yuanb/dd20emu/capture/WRData flux.png

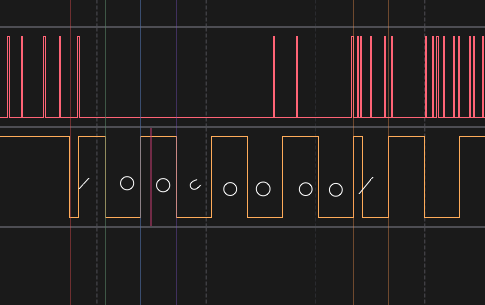
capture/WRData flux.png
