yuanb/dd20emu/dd20emu/rddata.ino

/*
    DD-20 emulator
    Copyright (C) 2020-2023 https://github.com/yuanb/dd20emu

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
    You should have received a copy of the GNU General Public License
    along with this program.  If not, see <https://www.gnu.org/licenses/>.
*/

//Tested values
//FM encoded 0 : ___n__________n___ : 1us + 31.2us + 1us (next bit)
//FM encoded 1 : ___n___n______n___ : 1us + 11 us + 1us + 19.2 us + 1us (next bit)

#define _delayNanoseconds(__ns)     __builtin_avr_delay_cycles( (double)(F_CPU)*((double)__ns)/1.0e9 /*+ 0.5 */)

#define delay_1us     _delayNanoseconds(1000)
#define delay_11us    _delayNanoseconds(11000)
#define delay_19_2us  _delayNanoseconds(19200)
#define delay_31_2us  _delayNanoseconds(31200)
#define pulse_1us   RD_HIGH; delay_1us; RD_LOW

#define RD_DATA_MASK   (1<<RD_DATA_BIT)
#define RD_HIGH   PORT_RDDATA |= RD_DATA_MASK;
#define RD_LOW    PORT_RDDATA &= ~RD_DATA_MASK;

#define FM_BIT_1  delay_11us; pulse_1us; delay_19_2us;
#define FM_BIT_0  delay_31_2us;

#define FM_ENCODE_BIT(v,m) {  if (v & m) { FM_BIT_1; } else { FM_BIT_0; } }
#define FM_OUTPUT_BIT(v,m) { pulse_1us; FM_ENCODE_BIT(v,m); }

extern uint8_t fdc_sector[SECSIZE_VZ];
extern vzdisk* vzdsk;

const uint8_t bitmask[8] = {
  0b10000000,
  0b01000000,
  0b00100000,
  0b00010000,
  0b00001000,
  0b00000100,
  0b00000010,
  0b00000001
};

bool handle_datastream() {
  static uint8_t current_sector = 0;
  static bool led = true;

  if (!drv_enabled || write_request || !vzdsk)
    return false;

  uint8_t tr = vtech1_track_x2/2;
  if (!vzdsk->get_sector(tr, current_sector)) {
    serial_log(PSTR("failed on reading sector TR: %d, :SEC: %d"), tr, current_sector);
    return false;
  }
    
  digitalWrite(LED_BUILTIN, led);
  led = !led;

  for(uint8_t i=0; i< SECSIZE_VZ; i++) {

    for(uint8_t j=0; j<8; j++) {
      if (write_request) {
        return false;
      }
      FM_OUTPUT_BIT(fdc_sector[i], bitmask[j]);


//      TODO: Faster code to stop RDDATA output when /wrreq
//      if (fdc_sector[i] & bitmask[j]) {
//        //1
//        pulse_1us;
//        //delay_11us;
//        for(uint8_t k=0; k<7; k++) {
//          if (write_request) {
//            //tag /WR request
//            digitalWrite(9, HIGH);
//            digitalWrite(9,LOW);
//            return false;
//          }      
//          delay_1us;
//        }
//        
//        pulse_1us;
//        
//        //delay_20us;
//        for(uint8_t k=0; k<13; k++) {
//          if (write_request) {
//            //tag /WR request
//            digitalWrite(9, HIGH);
//            digitalWrite(9,LOW);
//            return false;
//          }      
//          delay_1us;
//        }
//      }
//      else {
//        //0
//        pulse_1us;
//        for(uint8_t k=0; k<20; k++) {
//          if (write_request) {
//            //tag /WR request
//            digitalWrite(9, HIGH);
//            digitalWrite(9,LOW);
//            return false;
//          }
//          delay_1us;
//        }
//      }
    }
  }
  if (++current_sector >= SEC_NUM)
    current_sector = 0;

  return true;
}
