yuanb/dd20emu/dd20emu/isr_steps.ino

/*
    DD-20 emulator
    Copyright (C) 2020-2023 https://github.com/yuanb/dd20emu

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
    You should have received a copy of the GNU General Public License
    along with this program.  If not, see <https://www.gnu.org/licenses/>.
*/

#include "vzdisk.h"

volatile uint8_t vtech1_fdc_latch = 0;
volatile uint8_t vtech1_track_x2 = 0;

//Used to calculate latch PHI
#define PHI0(n) (((n)>>PIN_STEP0_BIT)&1)
#define PHI1(n) (((n)>>PIN_STEP1_BIT)&1)
#define PHI2(n) (((n)>>PIN_STEP2_BIT)&1)
#define PHI3(n) (((n)>>PIN_STEP3_BIT)&1)
#define STEP3 (1<<PIN_STEP3_BIT)
#define STEP2 (1<<PIN_STEP2_BIT)
#define STEP1 (1<<PIN_STEP1_BIT)
#define STEP0 (1<<PIN_STEP0_BIT)

void handle_steps() {
  if (!drv_enabled)
    return;

  uint8_t data = PORT_STEP & 0x0F;

  //Track--, if current bit is shifted to right by 1, wrapped by 4 bits
//  if (data == STEP0 && PHI1(vtech1_fdc_latch) ||
//      data == STEP1 && PHI2(vtech1_fdc_latch) ||
//      data == STEP2 && PHI3(vtech1_fdc_latch) ||
//      data == STEP3 && PHI0(vtech1_fdc_latch))
  if ( (PHI0(data) && !(PHI1(data) || PHI2(data) || PHI3(data)) && PHI1(vtech1_fdc_latch)) ||
       (PHI1(data) && !(PHI0(data) || PHI2(data) || PHI3(data)) && PHI2(vtech1_fdc_latch)) ||
       (PHI2(data) && !(PHI0(data) || PHI1(data) || PHI3(data)) && PHI3(vtech1_fdc_latch)) ||
       (PHI3(data) && !(PHI0(data) || PHI1(data) || PHI2(data)) && PHI0(vtech1_fdc_latch)) )
  {
    if (vtech1_track_x2 > 0)
      vtech1_track_x2--;
  }
  //Track++, if current bit is shifted to left by 1, wrapped by 4 bits
//  else if (
//    data == STEP0 && PHI3(vtech1_fdc_latch) ||
//    data == STEP1 && PHI0(vtech1_fdc_latch) ||
//    data == STEP2 && PHI1(vtech1_fdc_latch) ||
//    data == STEP3 && PHI2(vtech1_fdc_latch))
  else if ( (PHI0(data) && !(PHI1(data) || PHI2(data) || PHI3(data)) && PHI3(vtech1_fdc_latch)) ||
            (PHI1(data) && !(PHI0(data) || PHI2(data) || PHI3(data)) && PHI0(vtech1_fdc_latch)) ||
            (PHI2(data) && !(PHI0(data) || PHI1(data) || PHI3(data)) && PHI1(vtech1_fdc_latch)) ||
            (PHI3(data) && !(PHI0(data) || PHI1(data) || PHI2(data)) && PHI2(vtech1_fdc_latch)) )
  {
    if ( vtech1_track_x2 < 2 * TRK_NUM )
      vtech1_track_x2++;
  }
  
  vtech1_fdc_latch = data;
}
